t3knomanzer/maxmix-hardware/Beta/R99/Knob/Knob v4.step

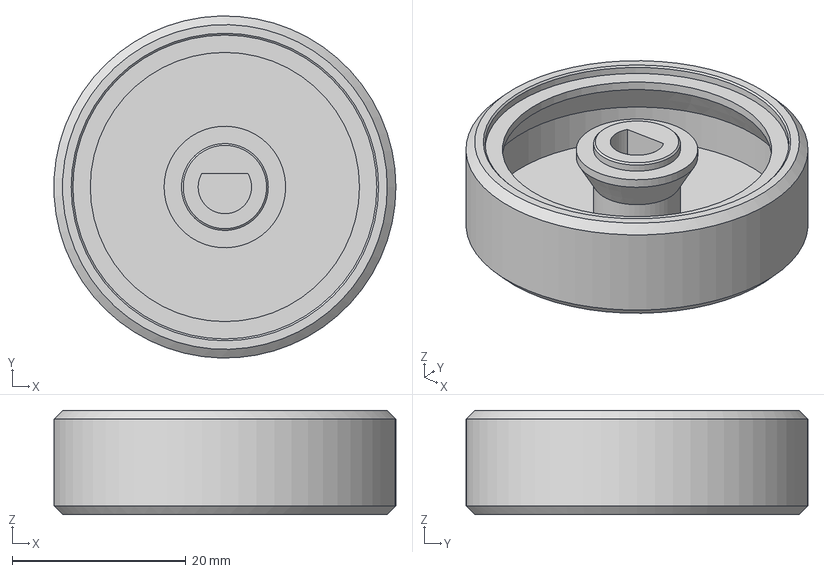
[picture p11: CAD file, 2020-10-10]
Beta/R99/Knob/Knob v4.step
39.4 x 39.4 x 12.0 mm
