t3knomanzer/maxmix-hardware/Beta/R99/LED Assembly - 8 bit - Shielded - Cells - Gap 0/LED Bracket - 8 bit - Shielded - Cells - Gap 0 v6.step

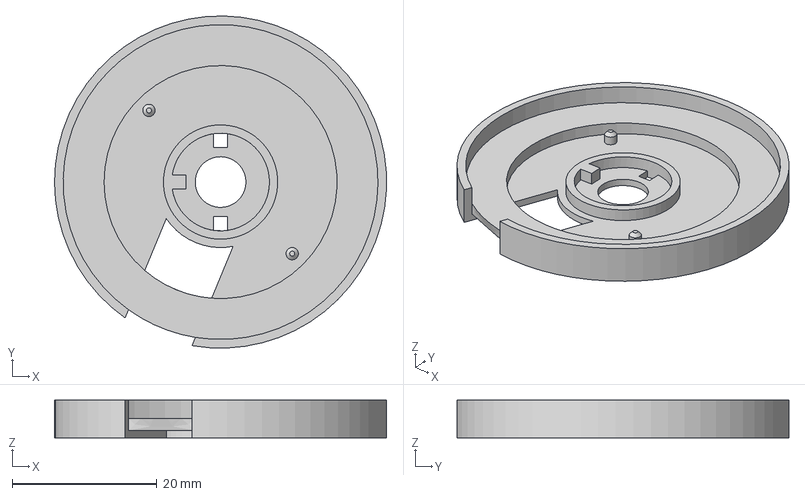
[picture p12: CAD file, 2020-10-10]
Beta/R99/LED Assembly - 8 bit - Shielded - Cells - Gap 0/LED Bracket - 8 bit - Shielded - Cells - Gap 0 v6.step
45.9 x 45.9 x 5.20 mm
