t3knomanzer/maxmix-hardware/Mods/LED Assembly - 12 bit - Shielded - Gap 0/LED Bracket - Adafruit 12 bit - Shielded - Gap 0 v14.step

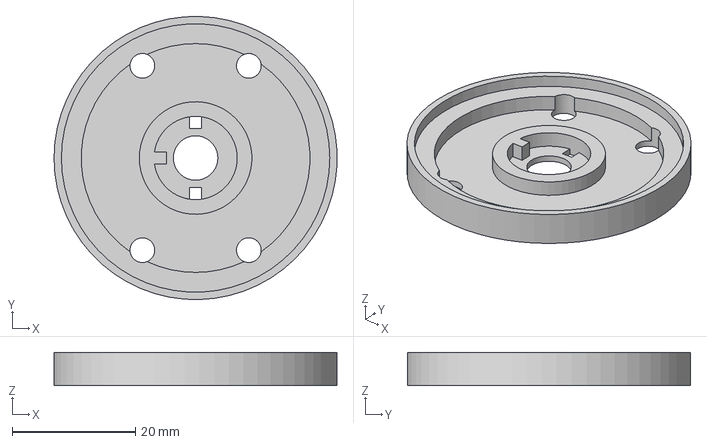
[picture p13: CAD file, 2020-10-10]
Mods/LED Assembly - 12 bit - Shielded - Gap 0/LED Bracket - Adafruit 12 bit - Shielded - Gap 0 v14.step
45.9 x 45.9 x 5.40 mm
