t3knomanzer/maxmix-hardware/Mods/LED Assembly - 12 bit - Shielded - LED 0/LED Cells - Adafruit 12 bit - LED 0 v2.step

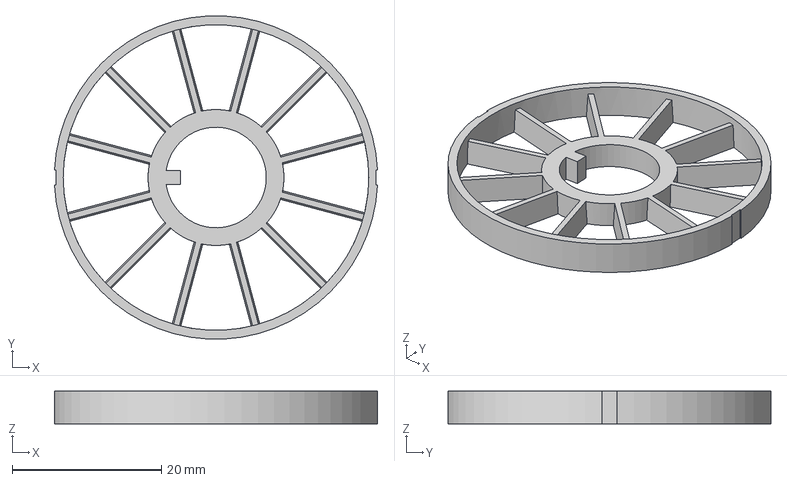
[picture p14: CAD file, 2020-10-10]
Mods/LED Assembly - 12 bit - Shielded - LED 0/LED Cells - Adafruit 12 bit - LED 0 v2.step
43.4 x 43.3 x 4.40 mm
