t3knomanzer/maxmix-hardware/Base/R98/Step/Maxmix_Base_LEDBracket_28mm_R98.step

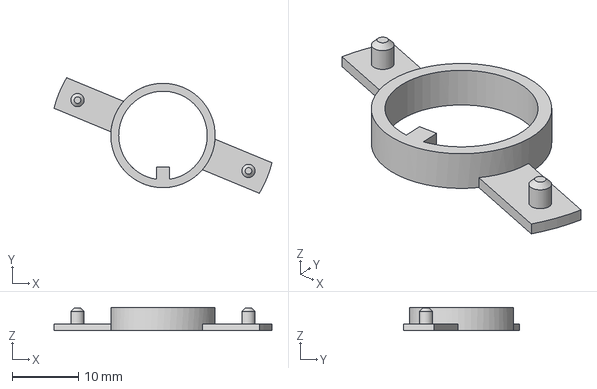
[picture p15: CAD file, 2020-09-22]
Base/R98/Step/Maxmix_Base_LEDBracket_28mm_R98.step
33.0 x 17.5 x 3.50 mm
