t3knomanzer/maxmix-hardware/Base/R99/Knob/Maxmix_Base_KnobCap_R99_v6.step

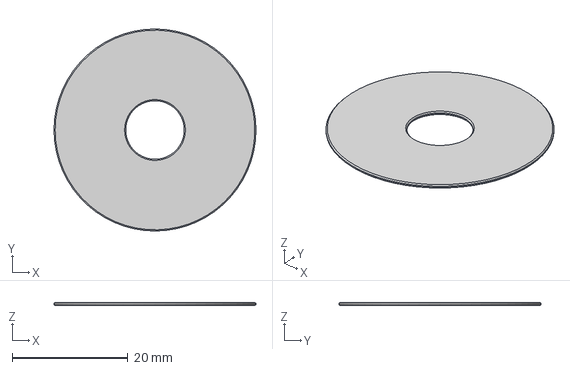
[picture p16: CAD file, 2020-10-10]
Base/R99/Knob/Maxmix_Base_KnobCap_R99_v6.step
34.9 x 34.9 x 0.6 mm
