t3knomanzer/maxmix-hardware/Base/R99/LEDAssembly/Maxmix_Base_LEDDiffuser_R99_v2.step

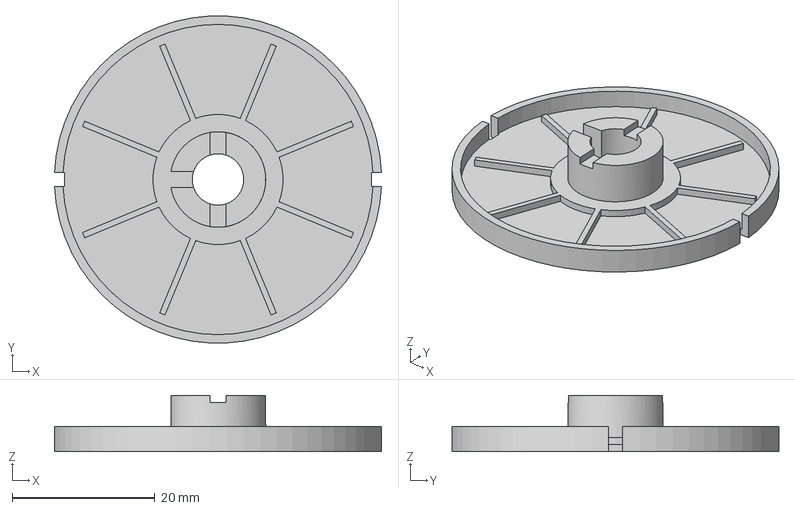
[picture p17: CAD file, 2020-10-10]
Base/R99/LEDAssembly/Maxmix_Base_LEDDiffuser_R99_v2.step
45.9 x 45.8 x 7.90 mm
