t3knomanzer/maxmix-hardware/Beta/12 bit Ring - Shielded/LED Diffuser - Adafruit 12 bit - Shielded v2.step

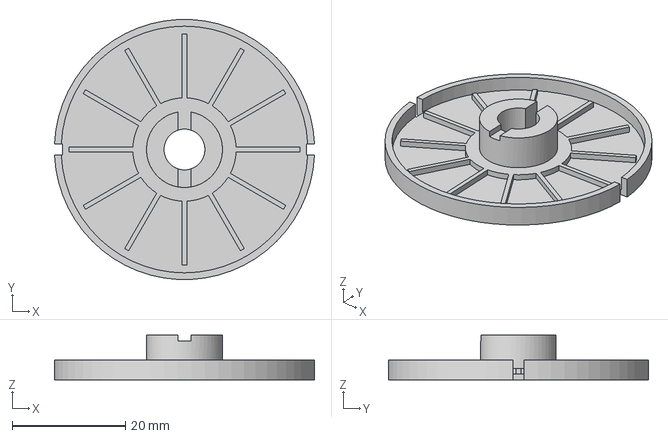
[picture p18: CAD file, 2020-10-01]
Beta/12 bit Ring - Shielded/LED Diffuser - Adafruit 12 bit - Shielded v2.step
45.9 x 45.8 x 7.90 mm
