t3knomanzer/maxmix-hardware/Base/R98/Step/Maxmix_Base_Knob_R98.step

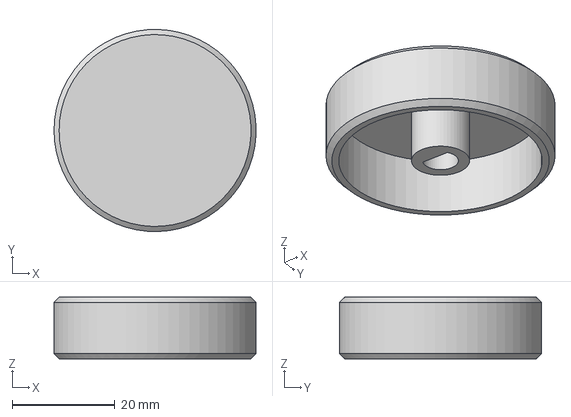
[picture p19: CAD file, 2020-09-22]
Base/R98/Step/Maxmix_Base_Knob_R98.step
39.4 x 39.4 x 12.0 mm
