t3knomanzer/maxmix-hardware/Base/R99/LEDAssembly/Maxmix_Base_LEDBracket_R99_v4.step

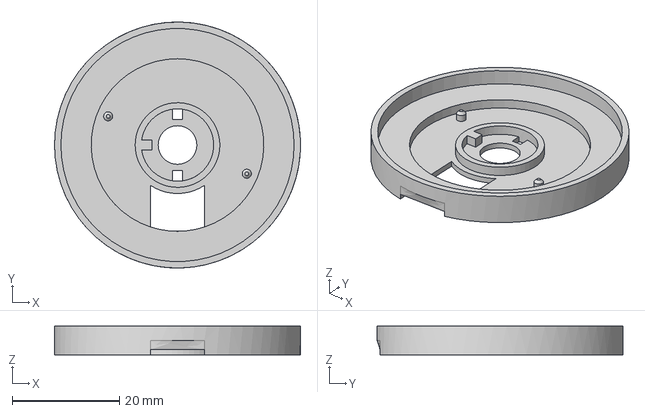
[picture p20: CAD file, 2020-10-10]
Base/R99/LEDAssembly/Maxmix_Base_LEDBracket_R99_v4.step
45.9 x 45.9 x 5.40 mm
