t3knomanzer/maxmix-hardware/Base/R98/Step/Maxmix_Base_Diffuser_R98.step

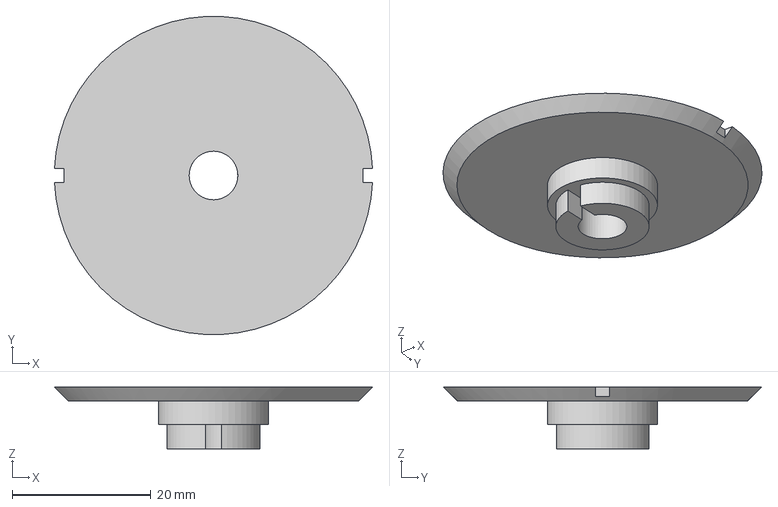
[picture p21: CAD file, 2020-09-22]
Base/R98/Step/Maxmix_Base_Diffuser_R98.step
45.8 x 45.8 x 8.90 mm
