t3knomanzer/maxmix-hardware/Base/R98/Step/Maxmix_Base_Tabs_R98.step

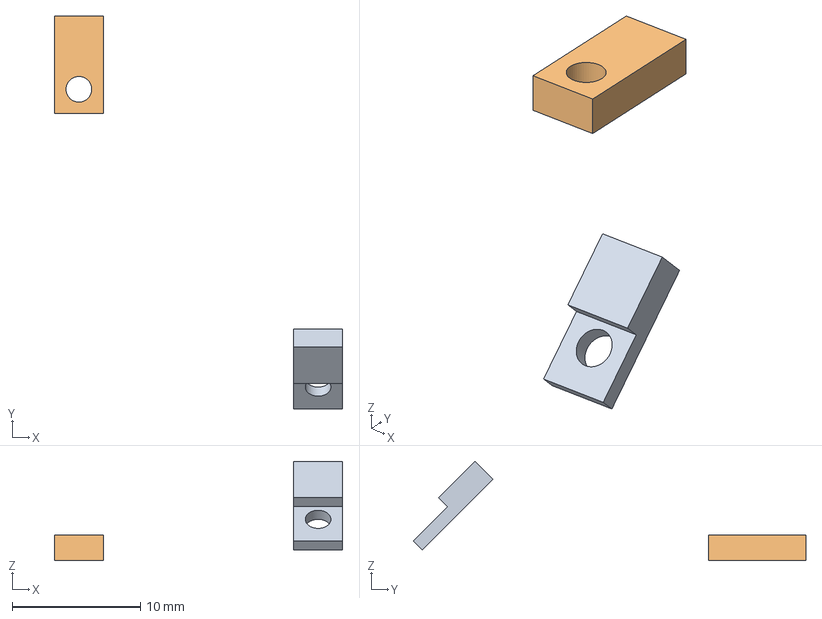
[picture p22: CAD file, 2020-09-22]
Base/R98/Step/Maxmix_Base_Tabs_R98.step
22.4 x 30.6 x 7.75 mm
