t3knomanzer/maxmix-hardware/Base/R98/Step/Maxmix_Base_Top_R98.step

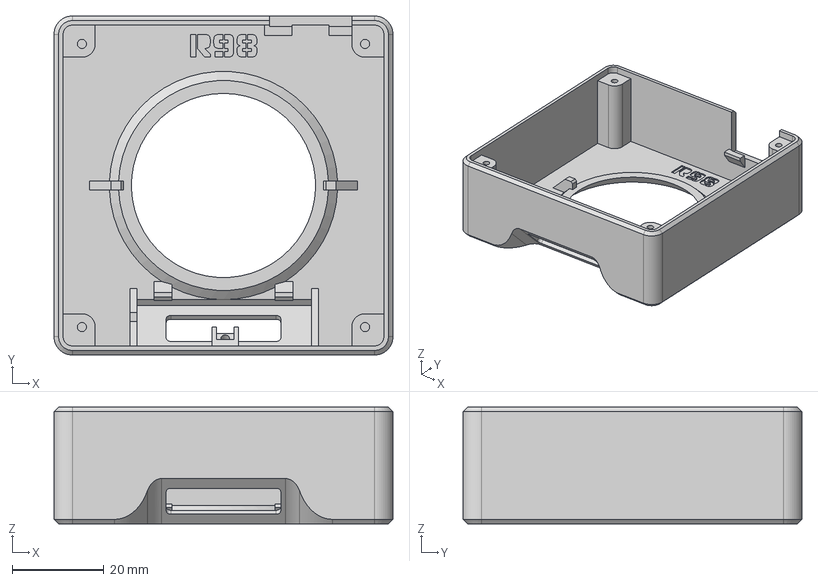
[picture p23: CAD file, 2020-09-22]
Base/R98/Step/Maxmix_Base_Top_R98.step
74.0 x 74.0 x 25.5 mm
