t3knomanzer/maxmix-hardware/Base/R98/Step/Maxmix_Base_Bottom_17mm_R98.step

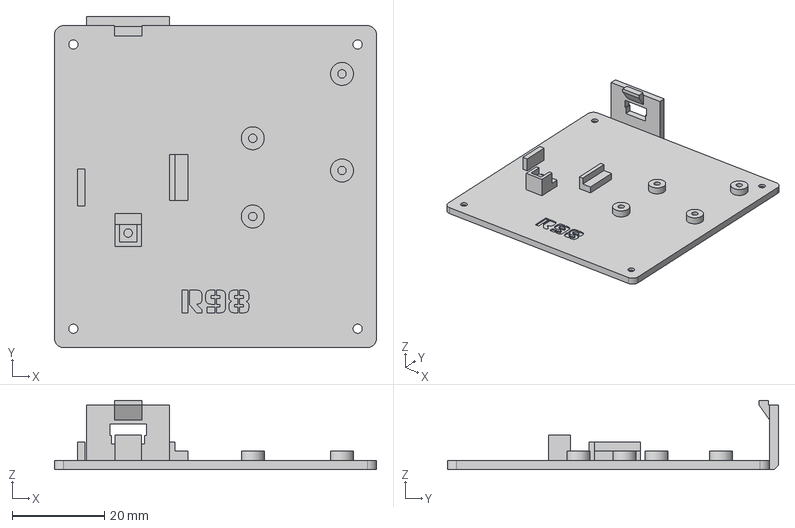
[picture p24: CAD file, 2020-09-22]
Base/R98/Step/Maxmix_Base_Bottom_17mm_R98.step
70.0 x 72.0 x 15.0 mm
